caccia78/PlancH/homeassistant/www/planch/planch-back.webp

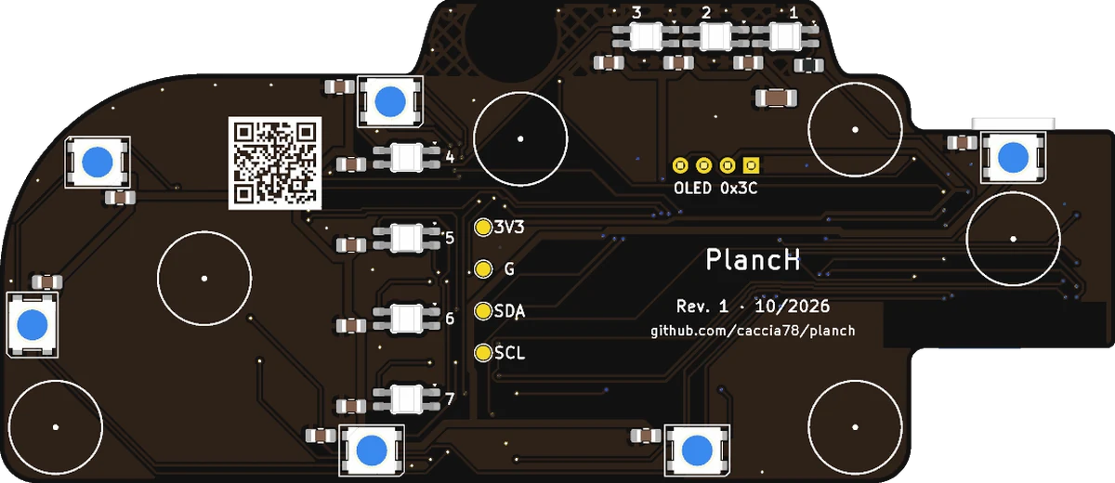
homeassistant/www/planch/planch-back.webp
