caccia78/PlancH/homeassistant/www/planch/planch-front.webp

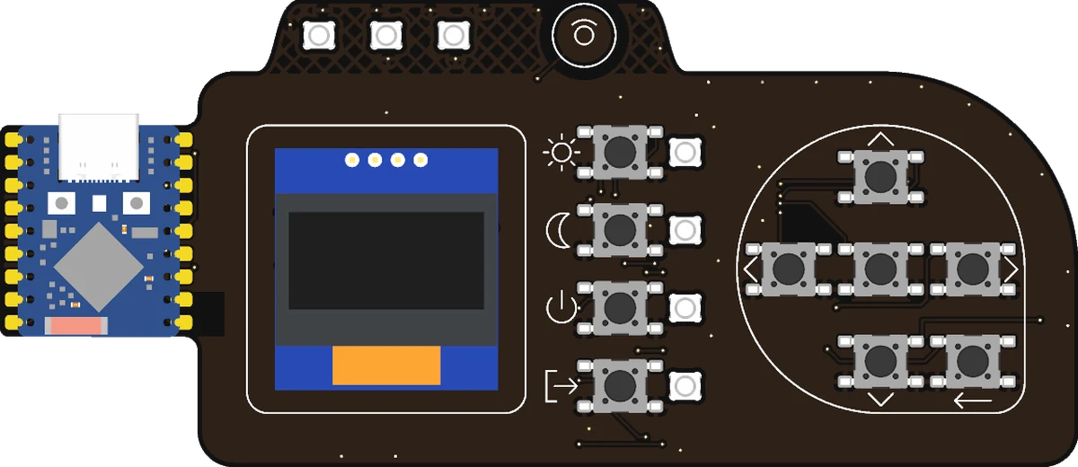
homeassistant/www/planch/planch-front.webp
