caccia78/PlancH/media/desk-stand-back.png

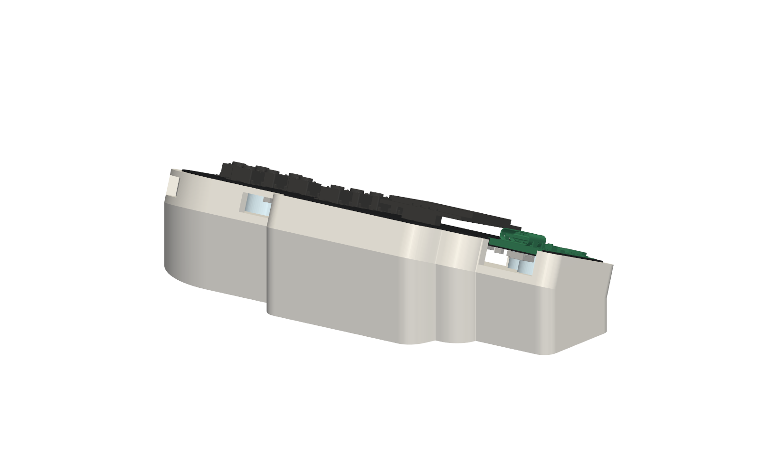
media/desk-stand-back.png
