caccia78/PlancH/media/desk-stand-side.png

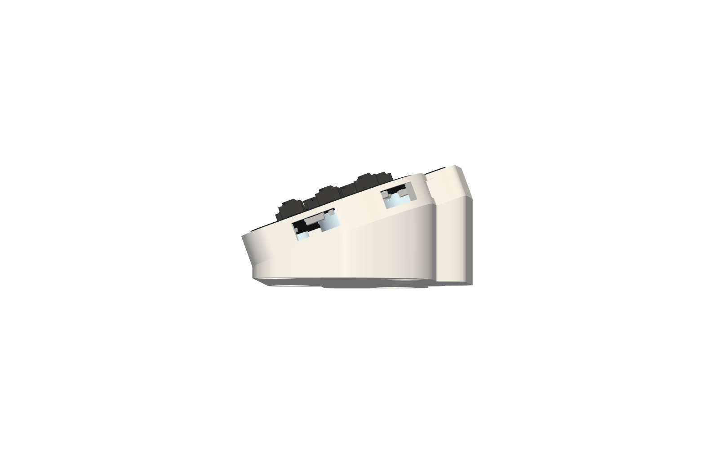
media/desk-stand-side.png
