caccia78/PlancH/media/wall-mount-side.png

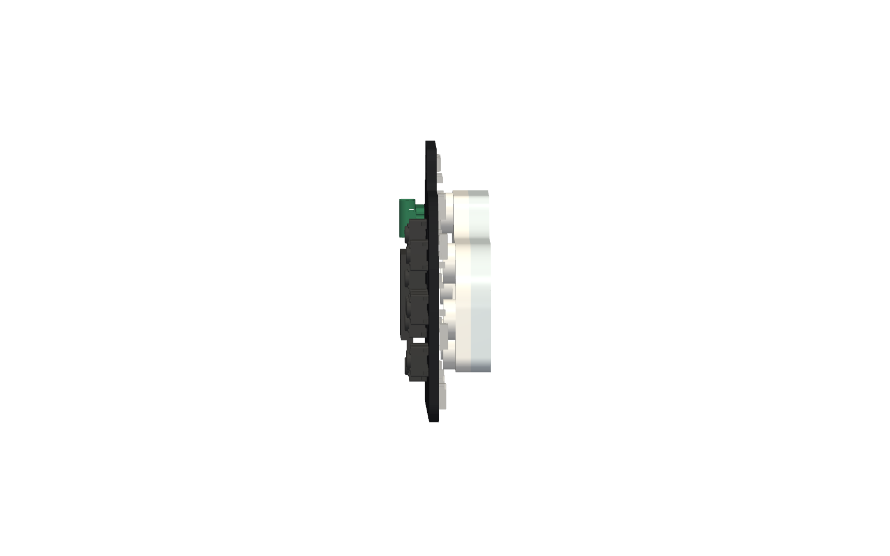
media/wall-mount-side.png
